tabiosg/gesturalguitareffect/src/fw/final/gesturalguitareffect/wah.audiogestural.cpp

#include "audiogestural.h"

void AudioEffectGesture::peakingCoefficients(float G, float fc, float Q, float fs) {

    float K = tan(M_PI * fc / fs);
    float V0 = pow(10, G / 20);
    float b0, b1, b2, a1, a2;
    if (G >= 0) {
      b0 = (1 + ((V0 / Q) * K) + pow(K, 2)) / (1 + ((1 / Q) * K) + pow(K, 2));
      b1 = (2 * (pow(K, 2) - 1)) / (1 + ((1 / Q) * K) + pow(K, 2));
      b2 = (1 - ((V0 / Q) * K) + pow(K, 2)) / (1 + ((1 / Q) * K) + pow(K, 2));
      a1 = b1;
      a2 = (1 - ((1 / Q) * K) + pow(K, 2)) / (1 + ((1 / Q) * K) + pow(K, 2));
    }
    else {
      b0 = (1 + ((1 / Q) * K) + pow(K, 2)) / (1 + ((V0 / Q) * K) + pow(K, 2));
      b1 = (2 * (pow(K, 2) - 1)) / (1 + ((V0 / Q) * K) + pow(K, 2));
      b2 = (1 - ((1 / Q) * K) + pow(K, 2)) / (1 + ((V0 / Q) * K) + pow(K, 2));
      a1 = b1;
      a2 = (1 - ((V0 / Q) * K) + pow(K, 2)) / (1 + ((V0 / Q) * K) + pow(K, 2));
    }

    // Assign the coefficients to the provided arrays
    mb0 = b0;
    mb1 = b1;
    mb2 = b2;
    ma1 = a1;
    ma2 = a2;
}

void AudioEffectGesture::applyPeakingCoefficients() {
  peakingCoefficients(mCurrentGain, mCurrentCenterFrequency, 1.0f, 44100.0f);
}

void AudioEffectGesture::applyBiquad(float32_t *input, float32_t *output, uint32_t blockSize) {
    static float32_t x1 = 0, x2 = 0; // Delay elements
    static float32_t y1 = 0, y2 = 0; // Delay elements
    
    float32_t b0, b1, b2, a1, a2;
    
    b0 = mb0; // Coefficients
    b1 = mb1;
    b2 = mb2;
    a1 = ma1;
    a2 = ma2;

    for (uint32_t i = 0; i < blockSize; i++) {
        // Calculate output using difference equation
        float32_t y0 = b0 * input[i] + b1 * x1 + b2 * x2 - a1 * y1 - a2 * y2;
        
        // Update delay elements
        x2 = x1;
        x1 = input[i];
        y2 = y1;
        y1 = y0;
        
        // Store filtered output
        output[i] = y0;
    }
}

int AudioEffectGesture::calculateGain(float input) {
  return map(input * GAIN_RESOLUTION, -GAIN_RESOLUTION, GAIN_RESOLUTION, MIN_GAIN, MAX_GAIN);
}

int AudioEffectGesture::calculateCenterFrequency(float input) {
  return map(input * CENTER_FREQUENCY_RESOLUTION, -CENTER_FREQUENCY_RESOLUTION, CENTER_FREQUENCY_RESOLUTION, MIN_CENTER_FREQUENCY, MAX_CENTER_FREQUENCY);
}
